Wudker/S.M.U/Software/LTspice/Draft1.asc

D1: diode; 1N5818
L1: ind; 100µ; Ipk=70 Rser=0.00095 Rpar=390 Cpar=5.277p
M1: nmos; IRFL4310
R1: res; 10; tol=0.1 pwr=0.25
V1: voltage; 3.3
V2: voltage; PULSE(0 15 0.1m 10u 10u 90m 100m 2)
Named nets: Vcc, Vster, 0, Vadc
.tran 0.8m
