Wudker/S.M.U/Software/LTspice/Draft2.asc

C1: cap; 1µ; V=50 Irms=0 Rser=0.0428 Lser=1.15p mfg="Würth Elektronik" pn="885382208005 WCAP-CSST 1206" type="X7R"
D1: diode; 1N5818
Komp: LT1011
L1: ind; 150µ; Ipk=0.26 Rser=0.86 Rpar=26100 Cpar=0 mfg="Bourns, Inc." pn="SRR4028-151Y"
M1: nmos; BSS145
OP: LT6016
R1: res; 10
R2: res; 470
R3: res; 7.6k
R4: res; 10k
R5: res; 120
R6: res; 1k
V1: voltage; 3.3
V2: voltage; PULSE(3.3 0 500u 10n 10n 10m 100m 1)
Named nets: 0, Vster, Vin, Vref, Vadc, Vop, Vraw
.tran 2m
