Wudker/S.M.U/Software/LTspice/Draft3.asc

R1: res; 1000; tol=0.1 pwr=0.25
R2: res; 100
V1: voltage; 3.3
Named nets: 0, Vin, ADC
.tran 1m
