Wudker/S.M.U/Software/LTspice/Pomiar_C.asc

C1: cap; 100µ
M1: pmos; IRLML6401
M2: nmos; 2N7002
R1: res; 1k; tol=0.1 pwr=0.25
R4: res; 4.7k
V1: voltage; 3.3
V2: voltage; PULSE(0 3.3 0 30u 30u 100m 1 2)
Named nets: Vcc, Vster, 0, Vadc
.tran 1
.model IRLML6401 PMOS(Level=1 Vto=-1.05 Kp=12.5 Lambda=0.02 Rd=0.05 Rs=0.05 Rg=10 Cgdmax=300p Cgdmin=50p Cgs=600p Cjo=200p Is=1e-14)
