Wudker/S.M.U/Software/LTspice/Pomiar_L.asc

C1: cap; 47n; V=250 Irms=0 Rser=0.0086 Lser=1.1n mfg="Würth Elektronik" pn="885342214002 WCAP-CSMH 2220" type="X7R"
C3: cap; 340p; V=100 Irms=10m Rser=43 Lser=0 mfg="Nichicon" pn="UPR2AR47MAH" type="Al electrolytic"
D1: diode; 1N5819
D2: diode; 1N4148
D3: diode; 1N4148
Komp: LT1011
L1: ind; 50µ; Ipk=0.26 Rser=0.86 Rpar=26100 Cpar=0 mfg="Bourns, Inc." pn="SRR4028-151Y"
M1: nmos; 2N7002
M2: pmos; FDC638P
R1: res; 50
R2: res; 10k
R3: res; 470
R4: res; 10k
R5: res; 680
R6: res; 10k
R7: res; 4.7k
R8: res; 4.7k
V1: voltage; 3.3
V2: voltage; PULSE(3.3 0 0.5m 3u 3u 5m 10m 3)
Named nets: 0, Vster, Vin, Vref, Vadc, Vraw, Vmos, V_clamped
.tran 2m
.model 1N6263W D(Is=120n N=1.05 Rs=1.2 Ikf=10m Cjo=2.2p M=0.33 Vj=0.6 mfg=Diodes_Inc type=Schottky)
